PatrickAJoseph/bluetooth-daq/software/bluetooth-daq-lp-em-cc2340r5/basic_ble_oad_onchip_LP_EM_CC2340R5_freertos_ticlang/app/app_main.c

/******************************************************************************

@file  app_main.c

@brief This file contains the application main functionality

Group: WCS, BTS
Target Device: cc23xx

******************************************************************************

 Copyright (c) 2022-2025, Texas Instruments Incorporated
 All rights reserved.

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
 *  Neither the name of Texas Instruments Incorporated nor the names of
    its contributors may be used to endorse or promote products derived
    from this software without specific prior written permission.

 THIS SOFTWARE IS PROVIDED BY THE COPYRIGHT HOLDERS AND CONTRIBUTORS "AS IS"
 AND ANY EXPRESS OR IMPLIED WARRANTIES, INCLUDING, BUT NOT LIMITED TO,
 THE IMPLIED WARRANTIES OF MERCHANTABILITY AND FITNESS FOR A PARTICULAR
 PURPOSE ARE DISCLAIMED. IN NO EVENT SHALL THE COPYRIGHT OWNER OR
 CONTRIBUTORS BE LIABLE FOR ANY DIRECT, INDIRECT, INCIDENTAL, SPECIAL,
 EXEMPLARY, OR CONSEQUENTIAL DAMAGES (INCLUDING, BUT NOT LIMITED TO,
 PROCUREMENT OF SUBSTITUTE GOODS OR SERVICES; LOSS OF USE, DATA, OR PROFITS;
 OR BUSINESS INTERRUPTION) HOWEVER CAUSED AND ON ANY THEORY OF LIABILITY,
 WHETHER IN CONTRACT, STRICT LIABILITY, OR TORT (INCLUDING NEGLIGENCE OR
 OTHERWISE) ARISING IN ANY WAY OUT OF THE USE OF THIS SOFTWARE,
 EVEN IF ADVISED OF THE POSSIBILITY OF SUCH DAMAGE.

******************************************************************************


*****************************************************************************/

//*****************************************************************************
//! Includes
//*****************************************************************************
#include "ti_ble_config.h"
#include "ti/ble/app_util/framework/bleapputil_api.h"
#include "ti/ble/app_util/menu/menu_module.h"
#include <app_main.h>

//*****************************************************************************
//! Defines
//*****************************************************************************

//*****************************************************************************
//! Globals
//*****************************************************************************

// Parameters that should be given as input to the BLEAppUtil_init function
BLEAppUtil_GeneralParams_t appMainParams =
{
    .taskPriority = 1,
    .taskStackSize = 1024,
    .profileRole = (BLEAppUtil_Profile_Roles_e)(HOST_CONFIG),
    .addressMode = DEFAULT_ADDRESS_MODE,
    .deviceNameAtt = attDeviceName,
    .pDeviceRandomAddress = pRandomAddress,
};

#if defined( HOST_CONFIG ) && ( HOST_CONFIG & ( PERIPHERAL_CFG | CENTRAL_CFG ) )
BLEAppUtil_PeriCentParams_t appMainPeriCentParams =
{
#if defined( HOST_CONFIG ) && ( HOST_CONFIG & ( PERIPHERAL_CFG ) )
 .connParamUpdateDecision = DEFAULT_PARAM_UPDATE_REQ_DECISION,
#endif //#if defined( HOST_CONFIG ) && ( HOST_CONFIG & ( PERIPHERAL_CFG ) )

#ifdef GAP_BOND_MGR
 .gapBondParams = &gapBondParams
#endif //GAP_BOND_MGR
};
#else //observer || broadcaster
BLEAppUtil_PeriCentParams_t appMainPeriCentParams;
#endif //#if defined( HOST_CONFIG ) && ( HOST_CONFIG & ( PERIPHERAL_CFG | CENTRAL_CFG ) )



//*****************************************************************************
//! Functions
//*****************************************************************************

/*********************************************************************
 * @fn      criticalErrorHandler
 *
 * @brief   Application task entry point
 *
 * @return  none
 */
void criticalErrorHandler(int32 errorCode , void* pInfo)
{
//    trace();
//
//#ifdef DEBUG_ERR_HANDLE
//
//    while (1);
//#else
//    SystemReset();
//#endif

}

/*********************************************************************
 * @fn      App_StackInitDone
 *
 * @brief   This function will be called when the BLE stack init is
 *          done.
 *          It should call the applications modules start functions.
 *
 * @return  none
 */
void App_StackInitDoneHandler(gapDeviceInitDoneEvent_t *deviceInitDoneData)
{
    bStatus_t status = SUCCESS;

    // Menu
    Menu_start();

    // Print the device ID address
    //MenuModule_printf(APP_MENU_DEVICE_ADDRESS, 0, "BLE ID Address: "
    //                  MENU_MODULE_COLOR_BOLD MENU_MODULE_COLOR_GREEN "%s" MENU_MODULE_COLOR_RESET,
    //                  BLEAppUtil_convertBdAddr2Str(deviceInitDoneData->devAddr));

    if ( appMainParams.addressMode > ADDRMODE_RANDOM)
    {
      // Print the RP address
      //  MenuModule_printf(APP_MENU_DEVICE_RP_ADDRESS, 0,
      //               "BLE RP Address: "
      //               MENU_MODULE_COLOR_BOLD MENU_MODULE_COLOR_GREEN "%s" MENU_MODULE_COLOR_RESET,
      //               BLEAppUtil_convertBdAddr2Str(GAP_GetDevAddress(FALSE)));
    }

#if defined( HOST_CONFIG ) && ( HOST_CONFIG & ( PERIPHERAL_CFG | CENTRAL_CFG ) )
    status = DevInfo_start();
    if(status != SUCCESS)
    {
        // TODO: Call Error Handler
    }
    status = SimpleGatt_start();
    if(status != SUCCESS)
    {
        // TODO: Call Error Handler
    }
#endif

#if defined( HOST_CONFIG ) && ( HOST_CONFIG & ( PERIPHERAL_CFG | CENTRAL_CFG ))  &&  defined(OAD_CFG)
    status =  OAD_start();
    if(status != SUCCESS)
    {
        // TODO: Call Error Handler
    }
#endif

#if defined( HOST_CONFIG ) && ( HOST_CONFIG & ( PERIPHERAL_CFG ) )
    // Any device that accepts the establishment of a link using
    // any of the connection establishment procedures referred to
    // as being in the Peripheral role.
    // A device operating in the Peripheral role will be in the
    // Peripheral role in the Link Layer Connection state.
    status = Peripheral_start();
    if(status != SUCCESS)
    {
        // TODO: Call Error Handler
    }
#endif

#if defined( HOST_CONFIG ) && ( HOST_CONFIG & ( BROADCASTER_CFG ) )
    // A device operating in the Broadcaster role is a device that
    // sends advertising events or periodic advertising events
    status = Broadcaster_start();
    if(status != SUCCESS)
    {
        // TODO: Call Error Handler
    }
#endif

#if defined( HOST_CONFIG ) && ( HOST_CONFIG & ( CENTRAL_CFG ) )
    // A device that supports the Central role initiates the establishment
    // of an active physical link. A device operating in the Central role will
    // be in the Central role in the Link Layer Connection state.
    // A device operating in the Central role is referred to as a Central.
    status = Central_start();
    if(status != SUCCESS)
    {
        // TODO: Call Error Handler
    }
#endif

#if defined( HOST_CONFIG ) && ( HOST_CONFIG & ( OBSERVER_CFG ) )
    // A device operating in the Observer role is a device that
    // receives advertising events or periodic advertising events
    status = Observer_start();
    if(status != SUCCESS)
    {
        // TODO: Call Error Handler
    }
#endif

#if defined( HOST_CONFIG ) && ( HOST_CONFIG & ( PERIPHERAL_CFG | CENTRAL_CFG ) )
    status = Connection_start();
    if(status != SUCCESS)
    {
        // TODO: Call Error Handler
    }
    status = Pairing_start();
    if(status != SUCCESS)
    {
        // TODO: Call Error Handler
    }
    status = Data_start();
    if(status != SUCCESS)
    {
        // TODO: Call Error Handler
    }

#if defined (BLE_V41_FEATURES) && (BLE_V41_FEATURES & L2CAP_COC_CFG)
    /* L2CAP COC Init */
    status = L2CAPCOC_start();
    if ( status != SUCCESS )
    {
    // TODO: Call Error Handler
    }
#endif //(BLE_V41_FEATURES) && (BLE_V41_FEATURES & L2CAP_COC_CFG)

#endif
}

/*********************************************************************
 * @fn      appMain
 *
 * @brief   Application main function
 *
 * @return  none
 */
void appMain(void)
{
    // Call the BLEAppUtil module init function
    BLEAppUtil_init(&criticalErrorHandler, &App_StackInitDoneHandler,
                    &appMainParams, &appMainPeriCentParams);
}
