PatrickAJoseph/bluetooth-daq/software/python/pybledaq/src/bdaq/core/initiator.py

from .packet import packet
from .parser import device
import socket
import serial
from bleak.backends.device import BLEDevice
from bleak import BleakScanner
from bleak import BleakClient
import asyncio
import time

from enum import Enum
from typing import IO

class InterfaceType(Enum):
    SOCKET = 0
    SERIAL = 1
    BLE    = 2

class initiator:
    
    interface: InterfaceType
    device: device
    file: str
    base_port: int
    iwrr_port: int
    irrw_port: int
    host: str
    iwrr_socket: socket.socket
    iwrr_listen_socket: socket.socket
    irrw_socket: socket.socket
    iwrr_address: tuple
    irrw_address: tuple
    serialHandle: serial.Serial
    bleDevice: BLEDevice

    async def BLE_init(self):
        # Scan for available BLE devices and determine if target device is available.

        bleDevices = await BleakScanner.discover()

        print("Initiator: BLE: Searching for BLE device with name: {_value}".format(_value = self.device.name))

        for bleDevice in bleDevices:

            print("Initiator: BLE: Current BLE device name: {_value}".format( _value = bleDevice.name ))

            if bleDevice.name == self.device.name:

                async with BleakClient(bleDevice) as client:

                    deviceSerialNumber = await client.read_gatt_char('0000fff8-0000-1000-8000-00805f9b34fb')
                    deviceID = await client.read_gatt_char('0000fff9-0000-1000-8000-00805f9b34fb')

                    _deviceSerialNumber = int.from_bytes(deviceSerialNumber)
                    _deviceID           = int.from_bytes(deviceID)

                    print("Initiator: BLE: Observed device serial number: {_value}".format( _value = _deviceSerialNumber))
                    print("Initiator: BLE: Observed device ID: {_value}".format( _value = _deviceID))

                    if( self.device.deviceSerialNumber == _deviceSerialNumber and self.device.number == _deviceID ):

                        print("Initiator: BLE: Device found !")
                        self.bleDevice = bleDevice
                        break


    def __init__(self, file:str, interface: InterfaceType):

        self.file = file
        self.interface = interface

        self.device = device(self.file)
        self.callback_table = []

        self.host = "127.0.0.1"
        self.base_port = self.device.baseport
        self.iwrr_port = self.base_port + 2*self.device.number
        self.irrw_port = self.base_port + 2*self.device.number + 1

        if( interface == InterfaceType.SOCKET ):
            
            print("Initiator: Opening a initiator socket server @ port {_port} and IP address {_ip}".format(_port = self.iwrr_port, _ip = self.host))

            self.iwrr_listen_socket = socket.socket( socket.AF_INET, socket.SOCK_STREAM )

            self.iwrr_listen_socket.bind( ( self.host, self.iwrr_port ) )

            print("Initiator: Completed binding initiator socket server @ port {_port}, IP address {_ip}".format(_port = self.iwrr_port, _ip = self.host))

            # Initiator write responder read.
            # Initiator is the socket server.
            # Responder is the socket client.

            print("Initiator: Started listening to incoming connections @ port {_port}, IP address {_ip}".format(_port = self.iwrr_port, _ip = self.host))

            self.iwrr_listen_socket.listen()

            print("Initiator: Got a connection request @ port {_port}, IP address {_ip}".format(_port = self.iwrr_port, _ip = self.host))

            # Wait for a responder to connect to this port.

            (self.iwrr_socket, self.irrw_address) = self.iwrr_listen_socket.accept()

            print("Initiator: Accepted a connection @ port {_port}, IP address {_ip}".format(_port = self.iwrr_port, _ip = self.host))

            # Initiator read responder write socket.
            # Initiator is the client.
            # Responder is the socket server.

            print("Initiator: Opening a initiator socket client @ port {_port}".format(_port = self.irrw_port))

            self.irrw_socket = socket.socket()
            self.irrw_socket.connect( ( self.host, self.irrw_port ) )

            print("Initiator: Connected to a initiator socket client @ port {_port}".format(_port = self.irrw_port))

        if( interface == InterfaceType.SERIAL ):

            self.serialHandle = serial.Serial( port = self.device.serialPort, baudrate = self.device.serialBaudRate, timeout = float(self.device.interfaceTimeoutMilliseconds) * 0.001 )

            if( self.serialHandle.is_open ):
                self.serialHandle.close()
            
            self.serialHandle.open()

            # Sending over this pattern flushes the responder's receive byte ring buffer.
            # This feature is availabe in C implementation of the SSCP responder.

            self.serialHandle.write("*1#".encode('utf-8'))

        if( interface == InterfaceType.BLE ):
            asyncio.run(self.BLE_init())

    def add_register_handle(self, reg: int, handle):

        is_unique = True

        for callback_entry in self.callback_table:

            try:
                if( callback_entry[0] == reg ):
                    is_unique = False
                    break
            except:
                break
        
        if(is_unique):
            self.callback_table.append( ( reg, handle ) )

    def stringify_packet(self, packet):

        s_packet = b''

        for p in packet:

            x = p.to_bytes(1)
            s_packet = s_packet + x

        return s_packet

    def unstringify_packet(self, packet: bytes):

        p = []

        for _p in packet:

            p.append(int(_p))
        
        return p

    def recv_exact(self, sock, size):
        data = b""
        while len(data) < size:
            chunk = sock.recv(size - len(data))
            if not chunk:
                raise ConnectionError("Socket closed")
            data += chunk
        return data

    async def BLE_read_register(self, name: str):

        async with BleakClient(self.bleDevice) as client:

            reg = self.device.get_register(name)

            p = packet()
            p.encode( device_id = self.device.number, ack = False, read = True, write = False, reg = reg.number, value = 0 )

            print("Initiator: BLE: Posting read request for register: {_name}".format(_name = name))

            await client.write_gatt_char('0000fff6-0000-1000-8000-00805f9b34fb', self.stringify_packet(p.bytes))

            print("Initiator: BLE: Requested for register: {_name}".format(_name = name))

            response = b'\x00\x00\x00\x00\x00\x00\x00\x00\x00\x00\x00\x00\x00\x00\x00\x00'

            while( response == b'\x00\x00\x00\x00\x00\x00\x00\x00\x00\x00\x00\x00\x00\x00\x00\x00'):
                response = await client.read_gatt_char('0000fff7-0000-1000-8000-00805f9b34fb')

            print("Initiator: BLE: Received response : {_response}".format(_response = self.stringify_packet(response)))

            print("Initiator: BLE: Response packet information.")

            response_packet = packet()

            ret = response_packet.decode(self.unstringify_packet(response))

            response_packet.info()

            if( ret == True ):

                print("Initiator: BLE: Response packet valid.")

                self.device.registers[response_packet.reg].set(response_packet.value)
            else:

                print("Initiator: BLE: Response packet invalid.")

                response_packet.info()

                pass



    def read_register(self, name: str):

        reg = self.device.get_register(name)

        p = packet()
        p.encode( device_id = self.device.number, ack = False, read = True, write = False, reg = reg.number, value = 0 )

        if( self.interface == InterfaceType.SOCKET ):

            print("Initiator: socket: Posting read request for register: {_name}".format(_name = name))

            self.iwrr_socket.sendall(self.stringify_packet(p.bytes))

            print("Initiator: socket: Requested for register: {_name}".format(_name = name))

            #response = self.irrw_socket.recv(16)

            response = self.recv_exact( self.irrw_socket, 16 )

            print("Initiator: socket: Received response : {_response}".format(_response = self.stringify_packet(response)))

            print("Initiator: socket: Response packet information.")

            response_packet = packet()

            ret = response_packet.decode(self.unstringify_packet(response))

            response_packet.info()

            if( ret == True ):

                print("Initiator: socket: Response packet valid.")

                self.device.registers[response_packet.reg].set(response_packet.value)
            else:

                print("Initiator: socket: Response packet invalid.")

                response_packet.info()

                pass

        if( self.interface == InterfaceType.SERIAL ):

            #print("Initiator: serial: Posting read request for register: {_name}".format(_name = name))

            self.serialHandle.write(self.stringify_packet(p.bytes))

            #print("Initiator: serial: Requested for register: {_name}".format(_name = name))

            response = self.serialHandle.read(16)

            #print("Initiator: serial: Received response : {_response}".format(_response = self.stringify_packet(response)))

            #print("Initiator: serial: Response packet information.")

            response_packet = packet()

            ret = response_packet.decode(self.unstringify_packet(response))

            #response_packet.info()

            if( ret == True ):

                #print("Initiator: serial: Response packet valid.")
                try:
                    self.device.registers[response_packet.reg].set(response_packet.value)
                except:
                    pass

                return True

            else:

                #print("Initiator: serial: Response packet invalid.")

                #response_packet.info()

                pass

                return False
        
        if( self.interface == InterfaceType.BLE ):
            asyncio.run(self.BLE_read_register(name))

    async def BLE_write_register(self, name: str, _value):
        
        reg = self.device.get_register(name)

        p = packet()
        p.encode( device_id = self.device.number, ack = False, read = False, write = True, reg = reg.number, value = _value )

        async with BleakClient(self.bleDevice) as client:

            print(self.stringify_packet(p.bytes))

            await client.write_gatt_char('0000fff6-0000-1000-8000-00805f9b34fb', self.stringify_packet(p.bytes) )

            #print("Initiator: BLE: Requested for register: {_name}".format(_name = name))

            response = b'\x00\x00\x00\x00\x00\x00\x00\x00\x00\x00\x00\x00\x00\x00\x00\x00'

            while( response == b'\x00\x00\x00\x00\x00\x00\x00\x00\x00\x00\x00\x00\x00\x00\x00\x00'):
                response = await client.read_gatt_char('0000fff7-0000-1000-8000-00805f9b34fb')

            if( len(response) != 16 ):

                #print("Initiator: BLE: Timeout event.")

                return False

            else:

                #print("Initiator: BLE: Timeout event did not occur.")

                pass

            #print("Initiator: BLE: Received response : {_response}".format(_response = self.stringify_packet(response)))

            #print("Initiator: BLE: Response packet information.")

            response_packet = packet()

            ret = response_packet.decode(self.unstringify_packet(response))

            response_packet.info()

            if( ret == True ):

                #print("Initiator: BLE: Response packet is valid.")

                pass

            else:

                #print("Initiator: BLE: Response packet is invalid !")

                #response_packet.info()

                ret = False

                pass

            return ret

    def write_register(self, name: str, _value: int ):

        reg = self.device.get_register(name)

        p = packet()
        p.encode( device_id = self.device.number, ack = False, read = False, write = True, reg = reg.number, value = _value )

        if( self.interface == InterfaceType.SOCKET ):

            #print("Initiator: socket: Posting write request for register: {_name}".format(_name = name))

            self.iwrr_socket.sendall(self.stringify_packet(p.bytes))

            #print("Initiator: socket: Requested for register: {_name}".format(_name = name))

            response = self.recv_exact( self.irrw_socket, 16 )

            #print("Initiator: socket: Received response : {_response}".format(_response = self.stringify_packet(response)))

            #print("Initiator: socket: Response packet information.")

            response_packet = packet()

            ret = response_packet.decode(self.unstringify_packet(response))

            response_packet.info()

            if( ret == True ):

                #print("Initiator: socket: Response packet is valid.")

                return True

                pass

            else:

                #print("Initiator: socket: Response packet is invalid !")

                #response_packet.info()

                return False

                pass


        if( self.interface == InterfaceType.SERIAL ):

            #print("Initiator: serial: Posting write request for register: {_name}".format(_name = name))

            #print("Initiator: serial: Packet to write {_packet}".format(_packet = self.stringify_packet(p.bytes)))

            self.serialHandle.write(self.stringify_packet(p.bytes))

            #print("Initiator: serial: Requested for register: {_name}".format(_name = name))

            response = self.serialHandle.read( 16 )

            if( len(response) != 16 ):

                #print("Initiator: serial: Timeout event.")

                return False

            else:

                #print("Initiator: serial: Timeout event did not occur.")

                pass

            #print("Initiator: serial: Received response : {_response}".format(_response = self.stringify_packet(response)))

            #print("Initiator: serial: Response packet information.")

            response_packet = packet()

            ret = response_packet.decode(self.unstringify_packet(response))

            #response_packet.info()

            if( ret == True ):

                #print("Initiator: serial: Response packet is valid.")

                pass

                return True

            else:

                #print("Initiator: serial: Response packet is invalid !")

                #response_packet.info()

                return False

                pass

        if( self.interface == InterfaceType.BLE ):
            return asyncio.run(self.BLE_write_register(name, _value))

    def set_parameter_value(self, name: str, value) -> bool:
        return self.device.set_parameter_value(name, value)
    
    def set_parameter_value_in_device(self, name: str, value) -> bool:

        ret = self.device.set_parameter_value(name, value)

        if self.device.get_parameter_register(name) is None:

            return False

        register_name = self.device.get_parameter_register(name).name
        register_value = self.device.get_parameter_register(name).value

        ret = self.write_register( register_name, register_value )

        return ret

    def get_parameter_value(self , name: str) -> bool:

        return self.device.get_parameter_value(name)

    def get_parameter_value_from_device(self, name: str):

        register = self.device.get_parameter_register(name)

        register_name = register.name

        ret = self.read_register( register_name )

        print("Reached here...")
        print(f"Return value: {ret}")

        if( ret == False ):
            return None

        value = self.device.get_parameter_value(name)

        print(value)

        return value
