PatrickAJoseph/bluetooth-daq/software/python/pybledaq/tests/bluetooth_daq_config.yml

defconfig:
  base_port: 3000
  device_number: '0'
  device_serial_number: 1
  interface_timeout_ms: '100'
  name: bluetooth_daq
  serial_baud_rate: 115200
  serial_port: COM13
regs:
  reg_0:
    comment: GPIO write register.
    name: GPIO_WRITE
    number: 0
    parameter_0:
      bitlength: 16
      max: 65535
      min: 0
      name: GPIO_write_value
      number: 0
      startbit: 0
      type: uint
    parameter_1:
      bitlength: 16
      max: 65535
      min: 0
      name: GPIO_write_value_reserved
      number: 1
      startbit: 16
      type: uint
  reg_1:
    comment: GPIO Toggle Register.
    name: GPIO_TOGGLE
    number: 1
    parameter_0:
      bitlength: 16
      max: 65535
      min: 0
      name: GPIO_toggle_value
      number: 0
      startbit: 0
      type: uint
    parameter_1:
      bitlength: 16
      max: 65535
      min: 0
      name: GPIO_toggle_value_reserved
      number: 1
      startbit: 16
      type: uint
  reg_10:
    comment: UART read data register.
    name: UART_READ_DATA
    number: 10
    parameter_0:
      bitlength: 8
      max: 255
      min: 0
      name: UART_READ_DATA_index
      number: 0
      startbit: 0
      type: uint
    parameter_1:
      bitlength: 8
      max: 255
      min: 0
      name: UART_READ_DATA_byte
      number: 1
      startbit: 8
      type: uint
    parameter_2:
      bitlength: 8
      max: 255
      min: 0
      name: UART_READ_DATA_read_count
      number: 2
      startbit: 16
      type: uint
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
      type: uint
    parameter_3:
      bitlength: 16
      max: 60000
      min: 0
      name: UART_TRANSFER_CONTROL_read_write_interval
      number: 3
      startbit: 4
      type: uint
    parameter_4:
      bitlength: 12
      max: 3
      min: 0
      name: UART_TRANSFER_CONTROL_reserved
      number: 4
      startbit: 20
      type: uint
